AlanCarvalhoEE/home-automation-platform/firmware/on_off_module/credentials_example.h

// Network parameters
const char* ssid = "*******";             // Network SSID
const char* password = "********";        // Network password
const char* brokerIP = "***.***.**.***";  // Broker IP
const uint16_t brokerPort = ****;         // Broker port

#define FW_SERVER_IP "***.***.*.**"       // Firmware update URL
#define FW_SERVER_PORT **                 // Firmware update port
